ZipCPU/arrowzip/rtl/arrowzip/cpu/icontrol.v

////////////////////////////////////////////////////////////////////////////////
//
// Filename:	icontrol.v
// {{{
// Project:	Zip CPU -- a small, lightweight, RISC CPU soft core
//
// Purpose:	An interrupt controller, for managing many interrupt sources.
//
//	This interrupt controller started from the question of how best to
//	design a simple interrupt controller.  As such, it has a few nice
//	qualities to it:
//		1. This is wishbone compliant
//		2. It sits on a 32-bit wishbone data bus
//		3. It only consumes one address on that wishbone bus.
//		4. There is no extra delays associated with reading this
//			device.
//		5. Common operations can all be done in one clock.
//
//	So, how shall this be used?  First, the 32-bit word is broken down as
//	follows:
//
//	Bit 31	- This is the global interrupt enable bit.  If set, interrupts
//		will be generated and passed on as they come in.
//	Bits 16-30	- These are specific interrupt enable lines.  If set,
//		interrupts from source (bit#-16) will be enabled.
//		To set this line and enable interrupts from this source, write
//		to the register with this bit set and the global enable set.
//		To disable this line, write to this register with global enable
//		bit not set, but this bit set.  (Writing a zero to any of these
//		bits has no effect, either setting or unsetting them.)
//	Bit 15 - This is the any interrupt pin.  If any interrupt is pending,
//		this bit will be set.
//	Bits 0-14	- These are interrupt bits.  When set, an interrupt is
//		pending from the corresponding source--regardless of whether
//		it was enabled.  (If not enabled, it won't generate an
//		interrupt, but it will still register here.)  To clear any
//		of these bits, write a '1' to the corresponding bit.  Writing
//		a zero to any of these bits has no effect.
//
//	The peripheral also sports a parameter, IUSED, which can be set
//	to any value between 1 and (buswidth/2-1, or) 15 inclusive.  This will
//	be the number of interrupts handled by this routine.  (Without the
//	parameter, Vivado was complaining about unused bits.  With it, we can
//	keep the complaints down and still use the routine).
//
//	To get access to more than 15 interrupts, chain these together, so
//	that one interrupt controller device feeds another.
//
//
// Creator:	Dan Gisselquist, Ph.D.
//		Gisselquist Technology, LLC
//
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
// This program is distributed in the hope that it will be useful, but WITHOUT
// ANY WARRANTY; without even the implied warranty of MERCHANTIBILITY or
// FITNESS FOR A PARTICULAR PURPOSE.  See the GNU General Public License
// for more details.
//
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
////////////////////////////////////////////////////////////////////////////////
//
`default_nettype	none
// }}}
module	icontrol(i_clk, i_reset, i_wb_stb, i_wb_we, i_wb_data,
		o_wb_ack, o_wb_stall, o_wb_data,
		i_brd_ints, o_interrupt);
	parameter	IUSED = 12, DW=32;
	input	wire			i_clk, i_reset;
	input	wire			i_wb_stb, i_wb_we;
	input	wire	[DW-1:0]	i_wb_data;
	output	wire			o_wb_ack, o_wb_stall;
	output	reg	[DW-1:0]	o_wb_data;
	input	wire	[(IUSED-1):0]	i_brd_ints;
	output	reg			o_interrupt;

	reg	[(IUSED-1):0]	r_int_state;
	reg	[(IUSED-1):0]	r_int_enable;
	reg			r_mie;
	wire			w_any;

	wire			wb_write, enable_ints, disable_ints;
	assign	wb_write     = (i_wb_stb)&&(i_wb_we);
	assign	enable_ints  = (wb_write)&&( i_wb_data[15]);
	assign	disable_ints = (wb_write)&&(!i_wb_data[15]);

	//
	// First step: figure out which interrupts have triggered.  An
	// interrupt "triggers" when the incoming interrupt wire is high, and
	// stays triggered until cleared by the bus.
	initial	r_int_state = 0;
	always @(posedge i_clk)
	if (i_reset)
		r_int_state  <= 0;
	else if (wb_write)
		r_int_state <= i_brd_ints
			| (r_int_state & (~i_wb_data[(IUSED-1):0]));
	else
		r_int_state <= (r_int_state | i_brd_ints);

	//
	// Second step: determine which interrupts are enabled.
	// Only interrupts that are enabled will be propagated forward on
	// the global interrupt line.
	initial	r_int_enable = 0;
	always @(posedge i_clk)
	if (i_reset)
		r_int_enable <= 0;
	else if (enable_ints)
		r_int_enable <= r_int_enable | i_wb_data[16 +: IUSED];
	else if (disable_ints)
		r_int_enable <= r_int_enable & (~ i_wb_data[16 +: IUSED]);

	//
	// Third step: The global interrupt enable bit.
	initial	r_mie = 1'b0;
	always @(posedge i_clk)
	if (i_reset)
		r_mie <= 1'b0;
	else if (enable_ints && i_wb_data[DW-1])
		r_mie <= 1'b1;
	else if (disable_ints && i_wb_data[DW-1])
		r_mie <= 1'b0;

	//
	// Have "any" enabled interrupts triggered?
	assign	w_any = ((r_int_state & r_int_enable) != 0);

	// How then shall the interrupt wire be set?
	initial	o_interrupt = 1'b0;
	always @(posedge i_clk)
	if (i_reset)
		o_interrupt <= 1'b0;
	else
		o_interrupt <= (r_mie)&&(w_any);

	//
	// Create the output data.  Place this into the next clock, to keep
	// it synchronous with w_any.
	initial	o_wb_data = 0;
	always @(posedge i_clk)
	begin
		o_wb_data <= 0;
		o_wb_data[31] <= r_mie;
		o_wb_data[15] <= w_any;

		o_wb_data[16 +: IUSED] <= r_int_enable;
		o_wb_data[ 0 +: IUSED] <= r_int_state;
	end

	// Make verilator happy
	generate if (IUSED < 15)
	begin
		// verilator lint_off UNUSED
		wire	[2*(15-IUSED)-1:0]	unused;
		assign	unused = { i_wb_data[32-2:(16+IUSED)],
				i_wb_data[16-2:IUSED] };
		// verilator lint_on  UNUSED

	end endgenerate

	assign	o_wb_ack = i_wb_stb;
	assign	o_wb_stall = 1'b0;


////////////////////////////////////////////////////////////////////////////////
////////////////////////////////////////////////////////////////////////////////
//
//
// Formal properties section
//
//
////////////////////////////////////////////////////////////////////////////////
////////////////////////////////////////////////////////////////////////////////
`ifdef	FORMAL
// Formal properties for this module are maintained elsewhere
`endif
endmodule
