ZipCPU/arrowzip/rtl/arrowzip/cpu/dcache.v

////////////////////////////////////////////////////////////////////////////////
//
// Filename:	dcache.v
// {{{
// Project:	Zip CPU -- a small, lightweight, RISC CPU soft core
//
// Purpose:	To provide a simple data cache for the ZipCPU.  The cache is
//		designed to be a drop in replacement for the pipememm memory
//	unit currently existing within the ZipCPU.  The goal of this unit is
//	to achieve single cycle read access to any memory in the last cache line
//	used, or two cycle access to any memory currently in the cache.
//
//	The cache separates between four types of accesses, one write and three
//	read access types.  The read accesses are split between those that are
//	not cacheable, those that are in the cache, and those that are not.
//
//	1. Write accesses always create writes to the bus.  For these reasons,
//		these may always be considered cache misses.
//
//		Writes to memory locations within the cache must also update
//		cache memory immediately, to keep the cache in synch.
//
//		It is our goal to be able to maintain single cycle write
//		accesses for memory bursts.
//
//	2. Read access to non-cacheable memory locations will also immediately
//		go to the bus, just as all write accesses go to the bus.
//
//	3. Read accesses to cacheable memory locations will immediately read
//		from the appropriate cache line.  However, since thee valid
//		line will take a second clock to read, it may take up to two
//		clocks to know if the memory was in cache.  For this reason,
//		we bypass the test for the last validly accessed cache line.
//
//		We shall design these read accesses so that reads to the cache
//		may take place concurrently with other writes to the bus.
//
//	Errors in cache reads will void the entire cache line.  For this reason,
//	cache lines must always be of a smaller in size than any associated
//	virtual page size--lest in the middle of reading a page a TLB miss
//	take place referencing only a part of the cacheable page.
//
//
//
//
// Creator:	Dan Gisselquist, Ph.D.
//		Gisselquist Technology, LLC
//
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
// This program is distributed in the hope that it will be useful, but WITHOUT
// ANY WARRANTY; without even the implied warranty of MERCHANTIBILITY or
// FITNESS FOR A PARTICULAR PURPOSE.  See the GNU General Public License
// for more details.
// }}}
// License:	GPL, v3, as defined and found on www.gnu.org,
// {{{
//		http://www.gnu.org/licenses/gpl.html
//
////////////////////////////////////////////////////////////////////////////////
//
`default_nettype	none
// }}}
module	dcache(i_clk, i_reset, i_pipe_stb, i_lock,
		i_op, i_addr, i_data, i_oreg,
			o_busy, o_pipe_stalled, o_valid, o_err, o_wreg,o_data,
		o_wb_cyc_gbl, o_wb_cyc_lcl, o_wb_stb_gbl, o_wb_stb_lcl,
			o_wb_we, o_wb_addr, o_wb_data, o_wb_sel,
		i_wb_ack, i_wb_stall, i_wb_err, i_wb_data
`ifdef	FORMAL
		, f_nreqs, f_nacks, f_outstanding, f_pc
`endif
	);
	parameter	LGCACHELEN = 8,
			ADDRESS_WIDTH=30,
			LGNLINES=(LGCACHELEN-3), // Log of the number of separate cache lines
			NAUX=5;	// # of aux d-wires to keep aligned w/memops
	parameter [0:0]	OPT_LOCAL_BUS=1'b1;
	parameter [0:0]	OPT_PIPE=1'b1;
	parameter [0:0]	OPT_LOCK=1'b1;
	parameter [0:0]	OPT_DUAL_READ_PORT=1'b1;
	parameter 	OPT_FIFO_DEPTH = 4;
	localparam	AW = ADDRESS_WIDTH; // Just for ease of notation below
	localparam	CS = LGCACHELEN; // Number of bits in a cache address
	localparam	LS = CS-LGNLINES; // Bits to spec position w/in cline
	parameter	F_LGDEPTH=1 + (((!OPT_PIPE)||(LS > OPT_FIFO_DEPTH))
					? LS : OPT_FIFO_DEPTH);
	localparam	LGAUX = 3; // log_2 of the maximum number of piped data
	localparam	DW = 32; // Bus data width
	localparam	DP = OPT_FIFO_DEPTH;
	//
	localparam [1:0]	DC_IDLE  = 2'b00; // Bus is idle
	localparam [1:0]	DC_WRITE = 2'b01; // Write
	localparam [1:0]	DC_READS = 2'b10; // Read a single value(!cachd)
	localparam [1:0]	DC_READC = 2'b11; // Read a whole cache line
	//
	input	wire		i_clk, i_reset;
	// Interface from the CPU
	input	wire		i_pipe_stb, i_lock;
	input	wire [2:0]		i_op;
	input	wire [(DW-1):0]	i_addr;
	input	wire [(DW-1):0]	i_data;
	input	wire [(NAUX-1):0] i_oreg; // Aux data, such as reg to write to
	// Outputs, going back to the CPU
	output	reg		o_busy;
	output	reg		o_pipe_stalled;
	output	reg		o_valid, o_err;
	output reg [(NAUX-1):0]	o_wreg;
	output	reg [(DW-1):0]	o_data;
	// Wishbone bus master outputs
	output	wire		o_wb_cyc_gbl, o_wb_cyc_lcl;
	output	reg		o_wb_stb_gbl, o_wb_stb_lcl;
	output	reg		o_wb_we;
	output	reg [(AW-1):0]	o_wb_addr;
	output	reg [(DW-1):0]	o_wb_data;
	output	wire [(DW/8-1):0] o_wb_sel;
	// Wishbone bus slave response inputs
	input	wire			i_wb_ack, i_wb_stall, i_wb_err;
	input	wire	[(DW-1):0]	i_wb_data;
	//
	// output	reg	[31:0]		o_debug;


	reg	cyc, stb, last_ack, end_of_line, last_line_stb;
	reg	r_wb_cyc_gbl, r_wb_cyc_lcl;
	// npending is the number of pending non-cached operations, counted
	// from the i_pipe_stb to the o_wb_ack
	reg	[DP:0]	npending;


	reg	[((1<<LGNLINES)-1):0] c_v;	// One bit per cache line, is it valid?
	reg	[(AW-LS-1):0]	c_vtags	[0:((1<<LGNLINES)-1)];
	reg	[(DW-1):0]	c_mem	[0:((1<<CS)-1)];
	reg			set_vflag;
	reg	[1:0]		state;
	reg	[(CS-1):0]	wr_addr;
	reg	[(DW-1):0]	cached_idata, cached_rdata;
	reg	[DW-1:0]	pre_data;
	reg			lock_gbl, lock_lcl;


	// To simplify writing to the cache, and the job of the synthesizer to
	// recognize that a cache write needs to take place, we'll take an extra
	// clock to get there, and use these c_w... registers to capture the
	// data in the meantime.
	reg			c_wr;
	reg	[(DW-1):0]	c_wdata;
	reg	[(DW/8-1):0]	c_wsel;
	reg	[(CS-1):0]	c_waddr;

	reg	[(AW-LS-1):0]	last_tag;
	reg			last_tag_valid;


	wire	[(LGNLINES-1):0]	i_cline;
	wire	[(CS-1):0]	i_caddr;

	assign	i_cline = i_addr[(CS+1):LS+2];
	assign	i_caddr = i_addr[(CS+1):2];

	wire	cache_miss_inow, w_cachable;
	assign	cache_miss_inow = (!last_tag_valid)
					||(last_tag != i_addr[(AW+1):LS+2])
					||(!c_v[i_cline]);

	wire	raw_cachable_address;

	iscachable chkaddress(i_addr[AW+1:2], raw_cachable_address);

	assign	w_cachable = ((!OPT_LOCAL_BUS)||(i_addr[(DW-1):(DW-8)]!=8'hff))
		&&((!i_lock)||(!OPT_LOCK))&&(raw_cachable_address);

	reg	r_cachable, r_svalid, r_dvalid, r_rd, r_cache_miss,
		r_rd_pending;
	reg	[(AW-1):0]		r_addr;
	wire	[(LGNLINES-1):0]	r_cline;
	wire	[(CS-1):0]		r_caddr;
	wire	[(AW-LS-1):0]		r_ctag;

	assign	r_cline = r_addr[(CS-1):LS];
	assign	r_caddr = r_addr[(CS-1):0];
	assign	r_ctag  = r_addr[(AW-1):LS];


	reg	wr_cstb, r_iv, in_cache;
	reg	[(AW-LS-1):0]	r_itag;
	reg	[DW/8-1:0]	r_sel;
	reg	[(NAUX+4-1):0]	req_data;
	reg			gie;



	//
	// The one-clock delayed read values from the cache.
	//
	initial	r_rd = 1'b0;
	initial	r_cachable = 1'b0;
	initial	r_svalid = 1'b0;
	initial	r_dvalid = 1'b0;
	initial	r_cache_miss = 1'b0;
	initial	r_addr = 0;
	initial	last_tag_valid = 0;
	initial	r_rd_pending = 0;
	always @(posedge i_clk)
	if (i_reset)
	begin
		r_rd <= 1'b0;
		r_cachable <= 1'b0;
		r_svalid <= 1'b0;
		r_dvalid <= 1'b0;
		r_cache_miss <= 1'b0;
		r_addr <= 0;
		r_rd_pending <= 0;
		last_tag_valid <= 0;
	end else begin
		// The single clock path
		// The valid for the single clock path
		//	Only ... we need to wait if we are currently writing
		//	to our cache.
		r_svalid<= (i_pipe_stb)&&(!i_op[0])&&(w_cachable)
				&&(!cache_miss_inow)&&(!c_wr)&&(!wr_cstb);

		//
		// The two clock in-cache path
		//
		// Some preliminaries that needed to be calculated on the first
		// clock
		if ((!o_pipe_stalled)&&(!r_rd_pending))
			r_addr <= i_addr[(AW+1):2];
		if ((!o_pipe_stalled)&&(!r_rd_pending))
		begin
			r_iv   <= c_v[i_cline];
			r_itag <= c_vtags[i_cline];
			r_cachable <= (!i_op[0])&&(w_cachable)&&(i_pipe_stb);
			r_rd_pending <= (i_pipe_stb)&&(!i_op[0])&&(w_cachable)
				&&((cache_miss_inow)||(c_wr)||(wr_cstb));
				// &&((!c_wr)||(!wr_cstb));
		end else begin
			r_iv   <= c_v[r_cline];
			r_itag <= c_vtags[r_cline];
			r_rd_pending <= (r_rd_pending)
				&&((!cyc)||(!i_wb_err))
				&&((r_itag != r_ctag)||(!r_iv));
		end
		r_rd <= (i_pipe_stb)&&(!i_op[0]);
		// r_itag contains the tag we didn't have available to us on the
		// last clock, r_ctag is a bit select from r_addr containing a
		// one clock delayed address.
		r_dvalid <= (!r_svalid)&&(!r_dvalid)&&(r_itag == r_ctag)&&(r_iv)
						&&(r_cachable)&&(r_rd_pending);
		if ((r_itag == r_ctag)&&(r_iv)&&(r_cachable)&&(r_rd_pending))
		begin
			last_tag_valid <= 1'b1;
			last_tag <= r_ctag;
		end else if ((state == DC_READC)
				&&(last_tag[CS-LS-1:0]==o_wb_addr[CS-1:LS])
				&&((i_wb_ack)||(i_wb_err)))
			last_tag_valid <= 1'b0;

		// r_cache miss takes a clock cycle.  It is only ever true for
		// something that should be cachable, but isn't in the cache.
		// A cache miss is only true _if_
		// 1. A read was requested
		// 2. It is for a cachable address, AND
		// 3. It isn't in the cache on the first read
		//	or the second read
		// 4. The read hasn't yet started to get this address
		r_cache_miss <= ((!cyc)||(o_wb_we))&&(r_cachable)
				// One clock path -- miss
				&&(!r_svalid)
				// Two clock path -- misses as well
				&&(r_rd)&&(!r_svalid)
				&&((r_itag != r_ctag)||(!r_iv));
	end

	initial	r_sel = 4'hf;
	always @(posedge i_clk)
	if (i_reset)
		r_sel <= 4'hf;
	else if (!o_pipe_stalled)
	begin
		casez({i_op[2:1], i_addr[1:0]})
		4'b0???: r_sel <= 4'b1111;
		4'b100?: r_sel <= 4'b1100;
		4'b101?: r_sel <= 4'b0011;
		4'b1100: r_sel <= 4'b1000;
		4'b1101: r_sel <= 4'b0100;
		4'b1110: r_sel <= 4'b0010;
		4'b1111: r_sel <= 4'b0001;
		endcase
	end

	assign	o_wb_sel = (state == DC_READC) ? 4'hf : r_sel;

	initial	o_wb_data = 0;
	always @(posedge i_clk)
	if (i_reset)
		o_wb_data <= 0;
	else if ((!o_busy)||((stb)&&(!i_wb_stall)))
	begin
		casez(i_op[2:1])
		2'b0?: o_wb_data <= i_data;
		2'b10: o_wb_data <= { (2){i_data[15:0]} };
		2'b11: o_wb_data <= { (4){i_data[ 7:0]} };
		endcase
	end

	generate if (OPT_PIPE)
	begin : OPT_PIPE_FIFO
		reg	[NAUX+4-2:0]	fifo_data [0:((1<<OPT_FIFO_DEPTH)-1)];

		reg	[DP:0]		wraddr, rdaddr;

		always @(posedge i_clk)
		if (i_pipe_stb)
			fifo_data[wraddr[DP-1:0]]
				<= { i_oreg[NAUX-2:0], i_op[2:1], i_addr[1:0] };

		always @(posedge i_clk)
		if (i_pipe_stb)
			gie <= i_oreg[NAUX-1];

`ifdef	NO_BKRAM
		reg	[NAUX+4-2:0]	r_req_data, r_last_data;
		reg			single_write;

		always @(posedge i_clk)
			r_req_data <= fifo_data[rdaddr[DP-1:0]];

		always @(posedge i_clk)
			single_write <= (rdaddr == wraddr)&&(i_pipe_stb);

		always @(posedge i_clk)
		if (i_pipe_stb)
			r_last_data <= { i_oreg[NAUX-2:0],
						i_op[2:1], i_addr[1:0] };

		always @(*)
		begin
			req_data[NAUX+4-1] = gie;
			// if ((r_svalid)||(state == DC_READ))
			if (single_write)
				req_data[NAUX+4-2:0] = r_last_data;
			else
				req_data[NAUX+4-2:0] = r_req_data;
		end

		always @(*)
			`ASSERT(req_data == fifo_data[rdaddr[DP-1:0]]);
`else
		always @(*)
			req_data[NAUX+4-2:0] = fifo_data[rdaddr[DP-1:0]];
		always @(*)
			req_data[NAUX+4-1] = gie;
`endif

		initial	wraddr = 0;
		always @(posedge i_clk)
		if ((i_reset)||((cyc)&&(i_wb_err)))
			wraddr <= 0;
		else if (i_pipe_stb)
			wraddr <= wraddr + 1'b1;

		initial	rdaddr = 0;
		always @(posedge i_clk)
		if ((i_reset)||((cyc)&&(i_wb_err)))
			rdaddr <= 0;
		else if ((r_dvalid)||(r_svalid))
			rdaddr <= rdaddr + 1'b1;
		else if ((state == DC_WRITE)&&(i_wb_ack))
			rdaddr <= rdaddr + 1'b1;
		else if ((state == DC_READS)&&(i_wb_ack))
			rdaddr <= rdaddr + 1'b1;


		always @(posedge i_clk)
			o_wreg <= req_data[(NAUX+4-1):4];

		/*
		reg	fifo_err;
		always @(posedge i_clk)
		begin
			fifo_err <= 1'b0;
			if ((!o_busy)&&(rdaddr != wraddr))
				fifo_err <= 1'b1;
			if ((!r_dvalid)&&(!r_svalid)&&(!r_rd_pending))
				fifo_err <= (npending != (wraddr-rdaddr));
		end

		always @(*)
		o_debug = { i_pipe_stb, state, cyc, stb,	//  5b
				fifo_err, i_oreg[3:0], o_wreg, 		// 10b
				rdaddr, wraddr, 		// 10b
				i_wb_ack, i_wb_err, o_pipe_stalled, o_busy,//4b
				r_svalid, r_dvalid, r_rd_pending };
		*/
	end else begin : NO_FIFO

		always @(posedge i_clk)
		if (i_pipe_stb)
			req_data <= { i_oreg, i_op[2:1], i_addr[1:0] };

		always @(*)
			o_wreg = req_data[(NAUX+4-1):4];


	end endgenerate
		


	initial	r_wb_cyc_gbl = 0;
	initial	r_wb_cyc_lcl = 0;
	initial	o_wb_stb_gbl = 0;
	initial	o_wb_stb_lcl = 0;
	initial	c_v = 0;
	initial	cyc = 0;
	initial	stb = 0;
	initial	c_wr = 0;
	initial	wr_cstb = 0;
	initial	state = DC_IDLE;
	initial	set_vflag = 1'b0;
	always @(posedge i_clk)
	if (i_reset)
	begin
		c_v <= 0;
		c_wr   <= 1'b0;
		c_wsel <= 4'hf;
		r_wb_cyc_gbl <= 1'b0;
		r_wb_cyc_lcl <= 1'b0;
		o_wb_stb_gbl <= 0;
		o_wb_stb_lcl <= 0;
		wr_cstb <= 1'b0;
		last_line_stb <= 1'b0;
		end_of_line <= 1'b0;
		state <= DC_IDLE;
		cyc <= 1'b0;
		stb <= 1'b0;
		state <= DC_IDLE;
		set_vflag <= 1'b0;
	end else begin
		// By default, update the cache from the write 1-clock ago
		// c_wr <= (wr_cstb)&&(wr_wtag == wr_vtag);
		// c_waddr <= wr_addr[(CS-1):0];
		c_wr <= 0;

		set_vflag <= 1'b0;
		if ((!cyc)&&(set_vflag))
			c_v[c_waddr[(CS-1):LS]] <= 1'b1;

		wr_cstb <= 1'b0;

		if (!cyc)
			wr_addr <= r_addr[(CS-1):0];
		else if (i_wb_ack)
			wr_addr <= wr_addr + 1'b1;
		else
			wr_addr <= wr_addr;

		if (LS <= 0)
			end_of_line <= 1'b1;
		else if (!cyc)
			end_of_line <= 1'b0;
		else if (!end_of_line)
		begin
			if (i_wb_ack)
				end_of_line
				<= (c_waddr[(LS-1):0] == {{(LS-2){1'b1}},2'b01});
			else
				end_of_line
				<= (c_waddr[(LS-1):0]=={{(LS-1){1'b1}}, 1'b0});
		end

		if (!cyc)
			last_line_stb <= (LS <= 0);
		else if ((stb)&&(!i_wb_stall)&&(LS <= 1))
			last_line_stb <= 1'b1;
		else if ((stb)&&(!i_wb_stall))
			last_line_stb <= (o_wb_addr[(LS-1):1]=={(LS-1){1'b1}});
		else if (stb)
			last_line_stb <= (o_wb_addr[(LS-1):0]=={(LS){1'b1}});

		//
		//
		if (state == DC_IDLE)
		begin
			o_wb_we <= 1'b0;

			cyc <= 1'b0;
			stb <= 1'b0;

			r_wb_cyc_gbl <= 1'b0;
			r_wb_cyc_lcl <= 1'b0;
			o_wb_stb_gbl <= 1'b0;
			o_wb_stb_lcl <= 1'b0;

			in_cache <= (i_op[0])&&(w_cachable);
			if ((i_pipe_stb)&&(i_op[0]))
			begin // Write  operation
				state <= DC_WRITE;
				o_wb_addr <= i_addr[(AW+1):2];
				o_wb_we <= 1'b1;

				cyc <= 1'b1;
				stb <= 1'b1;

				if (OPT_LOCAL_BUS)
				begin
				r_wb_cyc_gbl <= (i_addr[DW-1:DW-8]!=8'hff);
				r_wb_cyc_lcl <= (i_addr[DW-1:DW-8]==8'hff);
				o_wb_stb_gbl <= (i_addr[DW-1:DW-8]!=8'hff);
				o_wb_stb_lcl <= (i_addr[DW-1:DW-8]==8'hff);
				end else begin
					r_wb_cyc_gbl <= 1'b1;
					o_wb_stb_gbl <= 1'b1;
				end

			end else if (r_cache_miss)
			begin
				state <= DC_READC;
				o_wb_addr <= { r_ctag, {(LS){1'b0}} };

				c_waddr <= { r_ctag[CS-LS-1:0], {(LS){1'b0}} }-1'b1;
				cyc <= 1'b1;
				stb <= 1'b1;
				r_wb_cyc_gbl <= 1'b1;
				o_wb_stb_gbl <= 1'b1;
				wr_addr[LS-1:0] <= 0;
			end else if ((i_pipe_stb)&&(!w_cachable))
			begin // Read non-cachable memory area
				state <= DC_READS;
				o_wb_addr <= i_addr[(AW+1):2];

				cyc <= 1'b1;
				stb <= 1'b1;
				if (OPT_LOCAL_BUS)
				begin
				r_wb_cyc_gbl <= (i_addr[DW-1:DW-8]!=8'hff);
				r_wb_cyc_lcl <= (i_addr[DW-1:DW-8]==8'hff);
				o_wb_stb_gbl <= (i_addr[DW-1:DW-8]!=8'hff);
				o_wb_stb_lcl <= (i_addr[DW-1:DW-8]==8'hff);
				end else begin
				r_wb_cyc_gbl <= 1'b1;
				o_wb_stb_gbl <= 1'b1;
				end
			end // else we stay idle

		end else if (state == DC_READC)
		begin
			// We enter here once we have committed to reading
			// data into a cache line.
			if ((stb)&&(!i_wb_stall))
			begin
				stb <= (!last_line_stb);
				o_wb_stb_gbl <= (!last_line_stb);
				o_wb_addr[(LS-1):0] <= o_wb_addr[(LS-1):0]+1'b1;
			end

			if ((i_wb_ack)&&(!end_of_line))
				c_v[o_wb_addr[(CS-1):LS]] <= 1'b0;

			c_wr    <= (i_wb_ack);
			c_wdata <= i_wb_data;
			c_waddr <= ((i_wb_ack)?(c_waddr+1'b1):c_waddr);
			c_wsel  <= 4'hf;

			set_vflag <= !i_wb_err;
			if (i_wb_ack)
				c_vtags[r_addr[(CS-1):LS]]
						<= r_addr[(AW-1):LS];

			if (((i_wb_ack)&&(end_of_line))||(i_wb_err))
			begin
				state          <= DC_IDLE;
				cyc <= 1'b0;
				stb <= 1'b0;
				r_wb_cyc_gbl <= 1'b0;
				r_wb_cyc_lcl <= 1'b0;
				o_wb_stb_gbl <= 1'b0;
				o_wb_stb_lcl <= 1'b0;
				//
			end
		end else if (state == DC_READS)
		begin
			// We enter here once we have committed to reading
			// data that cannot go into a cache line
			if ((!i_wb_stall)&&(!i_pipe_stb))
			begin
				stb <= 1'b0;
				o_wb_stb_gbl <= 1'b0;
				o_wb_stb_lcl <= 1'b0;
			end

			if ((!i_wb_stall)&&(i_pipe_stb))
				o_wb_addr <= i_addr[(AW+1):2];

			c_wr <= 1'b0;

			if (((i_wb_ack)&&(last_ack))||(i_wb_err))
			begin
				state        <= DC_IDLE;
				cyc          <= 1'b0;
				stb          <= 1'b0;
				r_wb_cyc_gbl <= 1'b0;
				r_wb_cyc_lcl <= 1'b0;
				o_wb_stb_gbl <= 1'b0;
				o_wb_stb_lcl <= 1'b0;
			end
		end else if (state == DC_WRITE)
		begin
			c_wr    <= (stb)&&(c_v[o_wb_addr[CS-1:LS]])
				&&(c_vtags[o_wb_addr[CS-1:LS]]==o_wb_addr[AW-1:LS])
				&&(stb);
			c_wdata <= o_wb_data;
			c_waddr <= r_addr[CS-1:0];
			c_wsel  <= o_wb_sel;

			if ((!i_wb_stall)&&(!i_pipe_stb))
			begin
				stb          <= 1'b0;
				o_wb_stb_gbl <= 1'b0;
				o_wb_stb_lcl <= 1'b0;
			end

			wr_cstb  <= (stb)&&(!i_wb_stall)&&(in_cache);

			if ((stb)&&(!i_wb_stall))
				o_wb_addr <= i_addr[(AW+1):2];

			if (((i_wb_ack)&&(last_ack)
						&&((!OPT_PIPE)||(!i_pipe_stb)))
				||(i_wb_err))
			begin
				state        <= DC_IDLE;
				cyc          <= 1'b0;
				stb          <= 1'b0;
				r_wb_cyc_gbl <= 1'b0;
				r_wb_cyc_lcl <= 1'b0;
				o_wb_stb_gbl <= 1'b0;
				o_wb_stb_lcl <= 1'b0;
			end
		end
	end

	//
	// npending is the number of outstanding (non-cached) read or write
	// requests
	initial	npending = 0;
	always @(posedge i_clk)
	if ((i_reset)||(!OPT_PIPE)
			||((cyc)&&(i_wb_err))
			||((!cyc)&&(!i_pipe_stb))
			||(state == DC_READC))
		npending <= 0;
	else if (r_svalid)
		npending <= (i_pipe_stb) ? 1:0;
	else case({ (i_pipe_stb), (cyc)&&(i_wb_ack) })
	2'b01: npending <= npending - 1'b1;
	2'b10: npending <= npending + 1'b1;
	default: begin end
	endcase

	initial	last_ack = 1'b0;
	always @(posedge i_clk)
	if (i_reset)
		last_ack <= 1'b0;
	else if (state == DC_IDLE)
	begin
		last_ack <= 1'b0;
		if ((i_pipe_stb)&&(i_op[0]))
			last_ack <= 1'b1;
		else if (r_cache_miss)
			last_ack <= (LS == 0);
		else if ((i_pipe_stb)&&(!w_cachable))
			last_ack <= 1'b1;
	end else if (state == DC_READC)
	begin
		if (i_wb_ack)
			last_ack <= last_ack || (&wr_addr[LS-1:1]);
		else
			last_ack <= last_ack || (&wr_addr[LS-1:0]);
	end else case({ (i_pipe_stb), (i_wb_ack) })
	2'b01: last_ack <= (npending <= 2);
	2'b10: last_ack <= (!cyc)||(npending == 0);
	default: begin end
	endcase


	//
	// Writes to the cache
	//
	// These have been made as simple as possible.  Note that the c_wr
	// line has already been determined, as have the write value and address
	// on the last clock.  Further, this structure is defined to match the
	// block RAM design of as many architectures as possible.
	//
	always @(posedge i_clk)
	if (c_wr)
	begin
		if (c_wsel[0])
			c_mem[c_waddr][7:0] <= c_wdata[7:0];
		if (c_wsel[1])
			c_mem[c_waddr][15:8] <= c_wdata[15:8];
		if (c_wsel[2])
			c_mem[c_waddr][23:16] <= c_wdata[23:16];
		if (c_wsel[3])
			c_mem[c_waddr][31:24] <= c_wdata[31:24];
	end

	//
	// Reads from the cache
	//
	// Some architectures require that all reads be registered.  We
	// accomplish that here.  Whether or not the result of this read is
	// going to be our output will need to be determined with combinatorial
	// logic on the output.
	//
	generate if (OPT_DUAL_READ_PORT)
	begin

		always @(posedge i_clk)
			cached_idata <= c_mem[i_caddr];

		always @(posedge i_clk)
			cached_rdata <= c_mem[r_caddr];

	end else begin

		always @(posedge i_clk)
			cached_rdata <= c_mem[(o_busy) ? r_caddr : i_caddr];

		always @(*)
			cached_idata = cached_rdata;

	end endgenerate

// o_data can come from one of three places:
// 1. The cache, assuming the data was in the last cache line
// 2. The cache, second clock, assuming the data was in the cache at all
// 3. The cache, after filling the cache
// 4. The wishbone state machine, upon reading the value desired.
	always @(*)
		if (r_svalid)
			pre_data = cached_idata;
		else if (state == DC_READS)
			pre_data = i_wb_data;
		else
			pre_data = cached_rdata;

	always @(posedge i_clk)
	casez(req_data[3:0])
	4'b100?: o_data <= { 16'h0, pre_data[31:16] };
	4'b101?: o_data <= { 16'h0, pre_data[15: 0] };
	4'b1100: o_data <= { 24'h0, pre_data[31:24] };
	4'b1101: o_data <= { 24'h0, pre_data[23:16] };
	4'b1110: o_data <= { 24'h0, pre_data[15: 8] };
	4'b1111: o_data <= { 24'h0, pre_data[ 7: 0] };
	default	o_data <= pre_data;
	endcase

	initial	o_valid = 1'b0;
	always @(posedge i_clk)
	if (i_reset)
		o_valid <= 1'b0;
	else if (state == DC_READS)
		o_valid <= i_wb_ack;
	else
		o_valid <= (r_svalid)||(r_dvalid);

	initial	o_err = 1'b0;
	always @(posedge i_clk)
	if (i_reset)
		o_err <= 1'b0;
	else
		o_err <= (cyc)&&(i_wb_err);

	initial	o_busy = 0;
	always @(posedge i_clk)
	if ((i_reset)||((cyc)&&(i_wb_err)))
		o_busy <= 1'b0;
	else if (i_pipe_stb)
		o_busy <= 1'b1;
	else if ((state == DC_READS)&&(i_wb_ack))
		o_busy <= 1'b0;
	else if ((r_rd_pending)&&(!r_dvalid))
		o_busy <= 1'b1;
	else if ((state == DC_WRITE)
			&&(i_wb_ack)&&(last_ack)&&(!i_pipe_stb))
		o_busy <= 1'b0;
	else if (cyc)
		o_busy <= 1'b1;
	else // if ((r_dvalid)||(r_svalid))
		o_busy <= 1'b0;

	//
	// We can use our FIFO addresses to pre-calculate when an ACK is going
	// to be the last_noncachable_ack.


	always @(*)
	if (OPT_PIPE)
		o_pipe_stalled = (cyc)&&((!o_wb_we)||(i_wb_stall)||(!stb))
				||(r_rd_pending)||(npending[DP]);
	else
		o_pipe_stalled = o_busy;

	initial	lock_gbl = 0;
	initial	lock_lcl = 0;
	always @(posedge i_clk)
	if (i_reset)
	begin
		lock_gbl <= 1'b0;
		lock_lcl<= 1'b0;
	end else begin
		lock_gbl <= (OPT_LOCK)&&(i_lock)&&((r_wb_cyc_gbl)||(lock_gbl));
		lock_lcl <= (OPT_LOCK)&&(i_lock)&&((r_wb_cyc_lcl)||(lock_lcl));
	end

	assign	o_wb_cyc_gbl = (r_wb_cyc_gbl)||(lock_gbl);
	assign	o_wb_cyc_lcl = (r_wb_cyc_lcl)||(lock_lcl);

	generate if (AW+2 < DW)
	begin : UNUSED_BITS

		// Verilator lint_off UNUSED
		wire	[DW-AW-2:0]	unused;
		assign	unused = i_addr[DW-1:AW+1];
		// Verilator lint_on  UNUSED
	end endgenerate

`ifdef	FORMAL
// Formal properties for this module are maintained elsewhere
`endif
endmodule
