ZipCPU/arrowzip/rtl/arrowzip/cpu/memops.v

////////////////////////////////////////////////////////////////////////////////
//
// Filename:	memops.v
// {{{
// Project:	Zip CPU -- a small, lightweight, RISC CPU soft core
//
// Purpose:	A memory unit to support a CPU.
//
//	In the interests of code simplicity, this memory operator is
//	susceptible to unknown results should a new command be sent to it
//	before it completes the last one.  Unpredictable results might then
//	occurr.
//
//	20150919 -- Added support for handling BUS ERR's (i.e., the WB
//		error signal).
//
// Creator:	Dan Gisselquist, Ph.D.
//		Gisselquist Technology, LLC
//
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
// This program is distributed in the hope that it will be useful, but WITHOUT
// ANY WARRANTY; without even the implied warranty of MERCHANTIBILITY or
// FITNESS FOR A PARTICULAR PURPOSE.  See the GNU General Public License
// for more details.
//
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
////////////////////////////////////////////////////////////////////////////////
//
`default_nettype	none
// }}}
module	memops(i_clk, i_reset, i_stb, i_lock,
		i_op, i_addr, i_data, i_oreg,
			o_busy, o_valid, o_err, o_wreg, o_result,
		o_wb_cyc_gbl, o_wb_cyc_lcl,
			o_wb_stb_gbl, o_wb_stb_lcl,
			o_wb_we, o_wb_addr, o_wb_data, o_wb_sel,
		i_wb_ack, i_wb_stall, i_wb_err, i_wb_data
		);
	parameter	ADDRESS_WIDTH=30;
	parameter [0:0]	IMPLEMENT_LOCK=1'b1,
			WITH_LOCAL_BUS=1'b1,
			OPT_ALIGNMENT_ERR=1'b1,
			OPT_ZERO_ON_IDLE=1'b0;
	localparam	AW=ADDRESS_WIDTH;
	input	wire		i_clk, i_reset;
	input	wire		i_stb, i_lock;
	// CPU interface
	input	wire	[2:0]	i_op;
	input	wire	[31:0]	i_addr;
	input	wire	[31:0]	i_data;
	input	wire	[4:0]	i_oreg;
	// CPU outputs
	output	wire		o_busy;
	output	reg		o_valid;
	output	reg		o_err;
	output	reg	[4:0]	o_wreg;
	output	reg	[31:0]	o_result;
	// Wishbone outputs
	output	wire		o_wb_cyc_gbl;
	output	reg		o_wb_stb_gbl;
	output	wire		o_wb_cyc_lcl;
	output	reg		o_wb_stb_lcl;
	output	reg		o_wb_we;
	output	reg	[(AW-1):0]	o_wb_addr;
	output	reg	[31:0]	o_wb_data;
	output	reg	[3:0]	o_wb_sel;
	// Wishbone inputs
	input	wire		i_wb_ack, i_wb_stall, i_wb_err;
	input	wire	[31:0]	i_wb_data;

	reg	misaligned;

	generate if (OPT_ALIGNMENT_ERR)
	begin : GENERATE_ALIGNMENT_ERR
		always @(*)
		casez({ i_op[2:1], i_addr[1:0] })
		4'b01?1: misaligned = i_stb; // Words must be halfword aligned
		4'b0110: misaligned = i_stb; // Words must be word aligned
		4'b10?1: misaligned = i_stb; // Halfwords must be aligned
		// 4'b11??: misaligned <= 1'b0; Byte access are never misaligned
		default: misaligned = 1'b0;
		endcase
	end else
		always @(*)	misaligned = 1'b0;
	endgenerate

	reg	r_wb_cyc_gbl, r_wb_cyc_lcl;
	wire	gbl_stb, lcl_stb;
	assign	lcl_stb = (i_stb)&&(WITH_LOCAL_BUS!=0)&&(i_addr[31:24]==8'hff)
				&&(!misaligned);
	assign	gbl_stb = (i_stb)&&((WITH_LOCAL_BUS==0)||(i_addr[31:24]!=8'hff))
				&&(!misaligned);

	initial	r_wb_cyc_gbl = 1'b0;
	initial	r_wb_cyc_lcl = 1'b0;
	always @(posedge i_clk)
	if (i_reset)
	begin
		r_wb_cyc_gbl <= 1'b0;
		r_wb_cyc_lcl <= 1'b0;
	end else if ((r_wb_cyc_gbl)||(r_wb_cyc_lcl))
	begin
		if ((i_wb_ack)||(i_wb_err))
		begin
			r_wb_cyc_gbl <= 1'b0;
			r_wb_cyc_lcl <= 1'b0;
		end
	end else begin // New memory operation
		// Grab the wishbone
		r_wb_cyc_lcl <= (lcl_stb);
		r_wb_cyc_gbl <= (gbl_stb);
	end
	initial	o_wb_stb_gbl = 1'b0;
	always @(posedge i_clk)
	if (i_reset)
		o_wb_stb_gbl <= 1'b0;
	else if ((i_wb_err)&&(r_wb_cyc_gbl))
		o_wb_stb_gbl <= 1'b0;
	else if (o_wb_cyc_gbl)
		o_wb_stb_gbl <= (o_wb_stb_gbl)&&(i_wb_stall);
	else
		// Grab wishbone on any new transaction to the gbl bus
		o_wb_stb_gbl <= (gbl_stb);

	initial	o_wb_stb_lcl = 1'b0;
	always @(posedge i_clk)
	if (i_reset)
		o_wb_stb_lcl <= 1'b0;
	else if ((i_wb_err)&&(r_wb_cyc_lcl))
		o_wb_stb_lcl <= 1'b0;
	else if (o_wb_cyc_lcl)
		o_wb_stb_lcl <= (o_wb_stb_lcl)&&(i_wb_stall);
	else
		// Grab wishbone on any new transaction to the lcl bus
		o_wb_stb_lcl  <= (lcl_stb);

	reg	[3:0]	r_op;
	initial	o_wb_we   = 1'b0;
	initial	o_wb_data = 0;
	initial	o_wb_sel  = 0;
	always @(posedge i_clk)
	if (i_stb)
	begin
		o_wb_we   <= i_op[0];
		if (OPT_ZERO_ON_IDLE)
		begin
			casez({ i_op[2:1], i_addr[1:0] })
			4'b100?: o_wb_data <= { i_data[15:0], 16'h00 };
			4'b101?: o_wb_data <= { 16'h00, i_data[15:0] };
			4'b1100: o_wb_data <= {         i_data[7:0], 24'h00 };
			4'b1101: o_wb_data <= {  8'h00, i_data[7:0], 16'h00 };
			4'b1110: o_wb_data <= { 16'h00, i_data[7:0],  8'h00 };
			4'b1111: o_wb_data <= { 24'h00, i_data[7:0] };
			default: o_wb_data <= i_data;
			endcase
		end else
			casez({ i_op[2:1], i_addr[1:0] })
			4'b10??: o_wb_data <= { (2){ i_data[15:0] } };
			4'b11??: o_wb_data <= { (4){ i_data[7:0] } };
			default: o_wb_data <= i_data;
			endcase

		o_wb_addr <= i_addr[(AW+1):2];
		casez({ i_op[2:1], i_addr[1:0] })
		4'b01??: o_wb_sel <= 4'b1111;
		4'b100?: o_wb_sel <= 4'b1100;
		4'b101?: o_wb_sel <= 4'b0011;
		4'b1100: o_wb_sel <= 4'b1000;
		4'b1101: o_wb_sel <= 4'b0100;
		4'b1110: o_wb_sel <= 4'b0010;
		4'b1111: o_wb_sel <= 4'b0001;
		default: o_wb_sel <= 4'b1111;
		endcase
		r_op <= { i_op[2:1] , i_addr[1:0] };
	end else if ((OPT_ZERO_ON_IDLE)&&(!o_wb_cyc_gbl)&&(!o_wb_cyc_lcl))
	begin
		o_wb_we   <= 1'b0;
		o_wb_addr <= 0;
		o_wb_data <= 32'h0;
		o_wb_sel  <= 4'h0;
	end

	initial	o_valid = 1'b0;
	always @(posedge i_clk)
	if (i_reset)
		o_valid <= 1'b0;
	else
		o_valid <= (((o_wb_cyc_gbl)||(o_wb_cyc_lcl))
				&&(i_wb_ack)&&(!o_wb_we));
	initial	o_err = 1'b0;
	always @(posedge i_clk)
	if (i_reset)
		o_err <= 1'b0;
	else if ((r_wb_cyc_gbl)||(r_wb_cyc_lcl))
		o_err <= i_wb_err;
	else if ((i_stb)&&(!o_busy))
		o_err <= misaligned;
	else
		o_err <= 1'b0;

	assign	o_busy = (r_wb_cyc_gbl)||(r_wb_cyc_lcl);

	always @(posedge i_clk)
	if (i_stb)
		o_wreg    <= i_oreg;
	always @(posedge i_clk)
	if ((OPT_ZERO_ON_IDLE)&&(!i_wb_ack))
		o_result <= 32'h0;
	else begin
		casez(r_op)
		4'b01??: o_result <= i_wb_data;
		4'b100?: o_result <= { 16'h00, i_wb_data[31:16] };
		4'b101?: o_result <= { 16'h00, i_wb_data[15: 0] };
		4'b1100: o_result <= { 24'h00, i_wb_data[31:24] };
		4'b1101: o_result <= { 24'h00, i_wb_data[23:16] };
		4'b1110: o_result <= { 24'h00, i_wb_data[15: 8] };
		4'b1111: o_result <= { 24'h00, i_wb_data[ 7: 0] };
		default: o_result <= i_wb_data;
		endcase
	end

	reg	lock_gbl, lock_lcl;

	generate
	if (IMPLEMENT_LOCK != 0)
	begin

		initial	lock_gbl = 1'b0;
		initial	lock_lcl = 1'b0;

		always @(posedge i_clk)
		if (i_reset)
		begin
			lock_gbl <= 1'b0;
			lock_lcl <= 1'b0;
		end else if (((i_wb_err)&&((r_wb_cyc_gbl)||(r_wb_cyc_lcl)))
				||(misaligned))
		begin
			// Kill the lock if
			//	there's a bus error, or
			//	User requests a misaligned memory op
			lock_gbl <= 1'b0;
			lock_lcl <= 1'b0;
		end else begin
			// Kill the lock if
			//	i_lock goes down
			//	User starts on the global bus, then switches
			//	  to local or vice versa
			lock_gbl <= (i_lock)&&((r_wb_cyc_gbl)||(lock_gbl))
					&&(!lcl_stb);
			lock_lcl <= (i_lock)&&((r_wb_cyc_lcl)||(lock_lcl))
					&&(!gbl_stb);
		end

		assign	o_wb_cyc_gbl = (r_wb_cyc_gbl)||(lock_gbl);
		assign	o_wb_cyc_lcl = (r_wb_cyc_lcl)||(lock_lcl);
	end else begin

		assign	o_wb_cyc_gbl = (r_wb_cyc_gbl);
		assign	o_wb_cyc_lcl = (r_wb_cyc_lcl);

		always @(*)
			{ lock_gbl, lock_lcl } = 2'b00;

		// Make verilator happy
		// verilator lint_off UNUSED
		wire	[2:0]	lock_unused;
		assign	lock_unused = { i_lock, lock_gbl, lock_lcl };
		// verilator lint_on  UNUSED

	end endgenerate

	// Make verilator happy
	// verilator lint_off UNUSED
	generate if (AW < 22)
	begin : TOO_MANY_ADDRESS_BITS

		wire	[(21-AW):0] unused_addr;
		assign	unused_addr = i_addr[23:(AW+2)];

	end endgenerate
	// verilator lint_on  UNUSED

`ifdef	FORMAL
// Formal properties for this module are maintained elsewhere
`endif
endmodule
