ZipCPU/arrowzip/rtl/arrowzip/rxuartlite.v

////////////////////////////////////////////////////////////////////////////////
//
// Filename: 	rxuartlite.v
// {{{
// Project:	ArrowZip, a demonstration of the Arrow MAX1000 FPGA board
//
// Purpose:	Receive and decode inputs from a single UART line.
//
//
//	To interface with this module, connect it to your system clock,
//	and a UART input.  Set the parameter to the number of clocks per
//	baud.  When data becomes available, the o_wr line will be asserted
//	for one clock cycle.
//
//	This interface only handles 8N1 serial port communications.  It does
//	not handle the break, parity, or frame error conditions.
//
//
// Creator:	Dan Gisselquist, Ph.D.
//		Gisselquist Technology, LLC
//
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
// This program is distributed in the hope that it will be useful, but WITHOUT
// ANY WARRANTY; without even the implied warranty of MERCHANTIBILITY or
// FITNESS FOR A PARTICULAR PURPOSE.  See the GNU General Public License
// for more details.
//
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
// License:	GPL, v3, as defined and found on www.gnu.org,
//		http://www.gnu.org/licenses/gpl.html
//
//
////////////////////////////////////////////////////////////////////////////////
//
//
`default_nettype	none
// }}}
module rxuartlite #(
		// {{{
		parameter			TIMER_BITS = 10,
`ifdef	FORMAL
		parameter  [(TIMER_BITS-1):0]	CLOCKS_PER_BAUD = 16, // Necessary for formal proof
`else
		parameter  [(TIMER_BITS-1):0]	CLOCKS_PER_BAUD = 868,	// 115200 MBaud at 100MHz
`endif

		// }}}
	) (
		// {{{
		input	wire		i_clk,
		input	wire		i_uart_rx,
		output	reg		o_wr,
		output	reg	[7:0]	o_data
		// }}}
	);

	// Signal/register declarations
	// {{{
	localparam		TB = TIMER_BITS;
	//
	localparam [3:0]	RXUL_BIT_ZERO  = 4'h0;
	// Verilator lint_off UNUSED
	// These are used by the formal solver
	localparam [3:0]	RXUL_BIT_ONE   = 4'h1;
	localparam [3:0]	RXUL_BIT_TWO   = 4'h2;
	localparam [3:0]	RXUL_BIT_THREE = 4'h3;
	localparam [3:0]	RXUL_BIT_FOUR  = 4'h4;
	localparam [3:0]	RXUL_BIT_FIVE  = 4'h5;
	localparam [3:0]	RXUL_BIT_SIX   = 4'h6;
	localparam [3:0]	RXUL_BIT_SEVEN = 4'h7;
	// Verilator lint_on  UNUSED
	localparam [3:0]	RXUL_STOP      = 4'h8;
	localparam [3:0]	RXUL_WAIT      = 4'h9;
	localparam [3:0]	RXUL_IDLE      = 4'hf;
	wire	[(TB-1):0]	half_baud;
	reg	[3:0]		state;

	assign	half_baud = { 1'b0, CLOCKS_PER_BAUD[(TB-1):1] };
	reg	[(TB-1):0]	baud_counter;
	reg			zero_baud_counter;

	reg			q_uart, qq_uart, ck_uart;
	reg	[(TB-1):0]	chg_counter;
	reg			half_baud_time;
	reg	[7:0]		data_reg;
	// }}}

	// ck_uart
	// {{{
	// Since this is an asynchronous receiver, we need to register our
	// input a couple of clocks over to avoid any problems with 
	// metastability.  We do that here, and then ignore all but the
	// ck_uart wire.
	initial	q_uart  = 1'b1;
	initial	qq_uart = 1'b1;
	initial	ck_uart = 1'b1;
	always @(posedge i_clk)
		{ ck_uart, qq_uart, q_uart } <= { qq_uart, q_uart, i_uart_rx };
	// }}}

	// chg_counter
	// {{{
	// Keep track of the number of clocks since the last change.
	//
	// This is used to determine if we are in either a break or an idle
	// condition, as discussed further below.
	initial	chg_counter = {(TB){1'b1}};
	always @(posedge i_clk)
	if (qq_uart != ck_uart)
		chg_counter <= 0;
	else if (chg_counter != { (TB){1'b1} })
		chg_counter <= chg_counter + 1;
	// }}}

	// half_baud_time
	// {{{
	// Are we in the middle of a baud iterval?  Specifically, are we
	// in the middle of a start bit?  Set this to high if so.  We'll use
	// this within our state machine to transition out of the IDLE
	// state.
	initial	half_baud_time = 0;
	always @(posedge i_clk)
		half_baud_time <= (!ck_uart)&&(chg_counter >= half_baud-1'b1-1'b1);
	// }}}

	// state
	// {{{
	initial	state = RXUL_IDLE;
	always @(posedge i_clk)
	if (state == RXUL_IDLE)
	begin // Idle state, independent of baud counter
		// {{{
		// By default, just stay in the IDLE state
		state <= RXUL_IDLE;
		if ((!ck_uart)&&(half_baud_time))
			// UNLESS: We are in the center of a valid
			// start bit
			state <= RXUL_BIT_ZERO;
		// }}}
	end else if ((state >= RXUL_WAIT)&&(ck_uart))
		state <= RXUL_IDLE;
	else if (zero_baud_counter)
	begin
		// {{{
		if (state <= RXUL_STOP)
			// Data arrives least significant bit first.
			// By the time this is clocked in, it's what
			// you'll have.
			state <= state + 1;
		// }}}
	end
	// }}}

	// data_reg
	// {{{
	// Data bit capture logic.
	//
	// This is drastically simplified from the state machine above, based
	// upon: 1) it doesn't matter what it is until the end of a captured
	// byte, and 2) the data register will flush itself of any invalid
	// data in all other cases.  Hence, let's keep it real simple.
	always @(posedge i_clk)
	if ((zero_baud_counter)&&(state != RXUL_STOP))
		data_reg <= { qq_uart, data_reg[7:1] };
	// }}}

	// o_wr, o_data
	// {{{
	// Our data bit logic doesn't need nearly the complexity of all that
	// work above.  Indeed, we only need to know if we are at the end of
	// a stop bit, in which case we copy the data_reg into our output
	// data register, o_data, and tell others (for one clock) that data is
	// available.
	//
	initial	o_wr = 1'b0;
	initial	o_data = 8'h00;
	always @(posedge i_clk)
	if ((zero_baud_counter)&&(state == RXUL_STOP)&&(ck_uart))
	begin
		o_wr   <= 1'b1;
		o_data <= data_reg;
	end else
		o_wr   <= 1'b0;
	// }}}

	// baud_counter -- The baud counter
	// {{{
	// This is used as a "clock divider" if you will, but the clock needs
	// to be reset before any byte can be decoded.  In all other respects,
	// we set ourselves up for CLOCKS_PER_BAUD counts between baud
	// intervals.
	initial	baud_counter = 0;
	always @(posedge i_clk)
	if (((state==RXUL_IDLE))&&(!ck_uart)&&(half_baud_time))
		baud_counter <= CLOCKS_PER_BAUD-1'b1;
	else if (state == RXUL_WAIT)
		baud_counter <= 0;
	else if ((zero_baud_counter)&&(state < RXUL_STOP))
		baud_counter <= CLOCKS_PER_BAUD-1'b1;
	else if (!zero_baud_counter)
		baud_counter <= baud_counter-1'b1;
	// }}}

	// zero_baud_counter
	// {{{
	// Rather than testing whether or not (baud_counter == 0) within our
	// (already too complicated) state transition tables, we use
	// zero_baud_counter to pre-charge that test on the clock
	// before--cleaning up some otherwise difficult timing dependencies.
	initial	zero_baud_counter = 1'b1;
	always @(posedge i_clk)
	if ((state == RXUL_IDLE)&&(!ck_uart)&&(half_baud_time))
		zero_baud_counter <= 1'b0;
	else if (state == RXUL_WAIT)
		zero_baud_counter <= 1'b1;
	else if ((zero_baud_counter)&&(state < RXUL_STOP))
		zero_baud_counter <= 1'b0;
	else if (baud_counter == 1)
		zero_baud_counter <= 1'b1;
	// }}}
////////////////////////////////////////////////////////////////////////////////
////////////////////////////////////////////////////////////////////////////////
////////////////////////////////////////////////////////////////////////////////
//
// Formal properties
// {{{
////////////////////////////////////////////////////////////////////////////////
////////////////////////////////////////////////////////////////////////////////
////////////////////////////////////////////////////////////////////////////////
`ifdef	FORMAL
// Formal properties for this module are maintained elsewhere
`endif
// }}}
endmodule
