ZipCPU/arrowzip/rtl/arrowzip/cpu/wbwatchdog.v

////////////////////////////////////////////////////////////////////////////////
//
// Filename:	wbwatchdog.v
// {{{
// Project:	Zip CPU -- a small, lightweight, RISC CPU soft core
//
// Purpose:	A Zip timer, redesigned to be a bus watchdog
//
//	This is basically a timer, but there are some unique features to it.
//
//	1. There is no way to "write" the timeout to this watchdog.  It is
//		fixed with an input (that is assumed to be constant)
//	2. The counter returns to i_timer and the interrupt is cleared on any
//		reset.
//	3. Between resets, the counter counts down to zero.  Once (and if) it
//		hits zero, it will remain at zero until reset.
//	4. Any time the counter is at zero, and until the reset that resets
//		the counter, the output interrupt will be set.
//
//
// Creator:	Dan Gisselquist, Ph.D.
//		Gisselquist Technology, LLC
//
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
// This program is distributed in the hope that it will be useful, but WITHOUT
// ANY WARRANTY; without even the implied warranty of MERCHANTIBILITY or
// FITNESS FOR A PARTICULAR PURPOSE.  See the GNU General Public License
// for more details.
//
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
////////////////////////////////////////////////////////////////////////////////
//
`default_nettype	none
// }}}
module	wbwatchdog(i_clk, i_reset, i_timeout, o_int);
	parameter	BW = 32;
	input	wire		i_clk, i_reset;
	// Inputs (these were at one time wishbone controlled ...)
	input	wire [(BW-1):0]	i_timeout;
	// Interrupt line
	output	reg		o_int;
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
